DEVCOM-Armaments-Center/SUPI_V3.X/sUPI Electrical/Platform/PB-F-0213 Fusion - SUPI Platform-(src,fab,asm)/ASM-PB-F-0210 Fusion-Platform-[NO VARIATIONS]-A.6/Job1.PDF

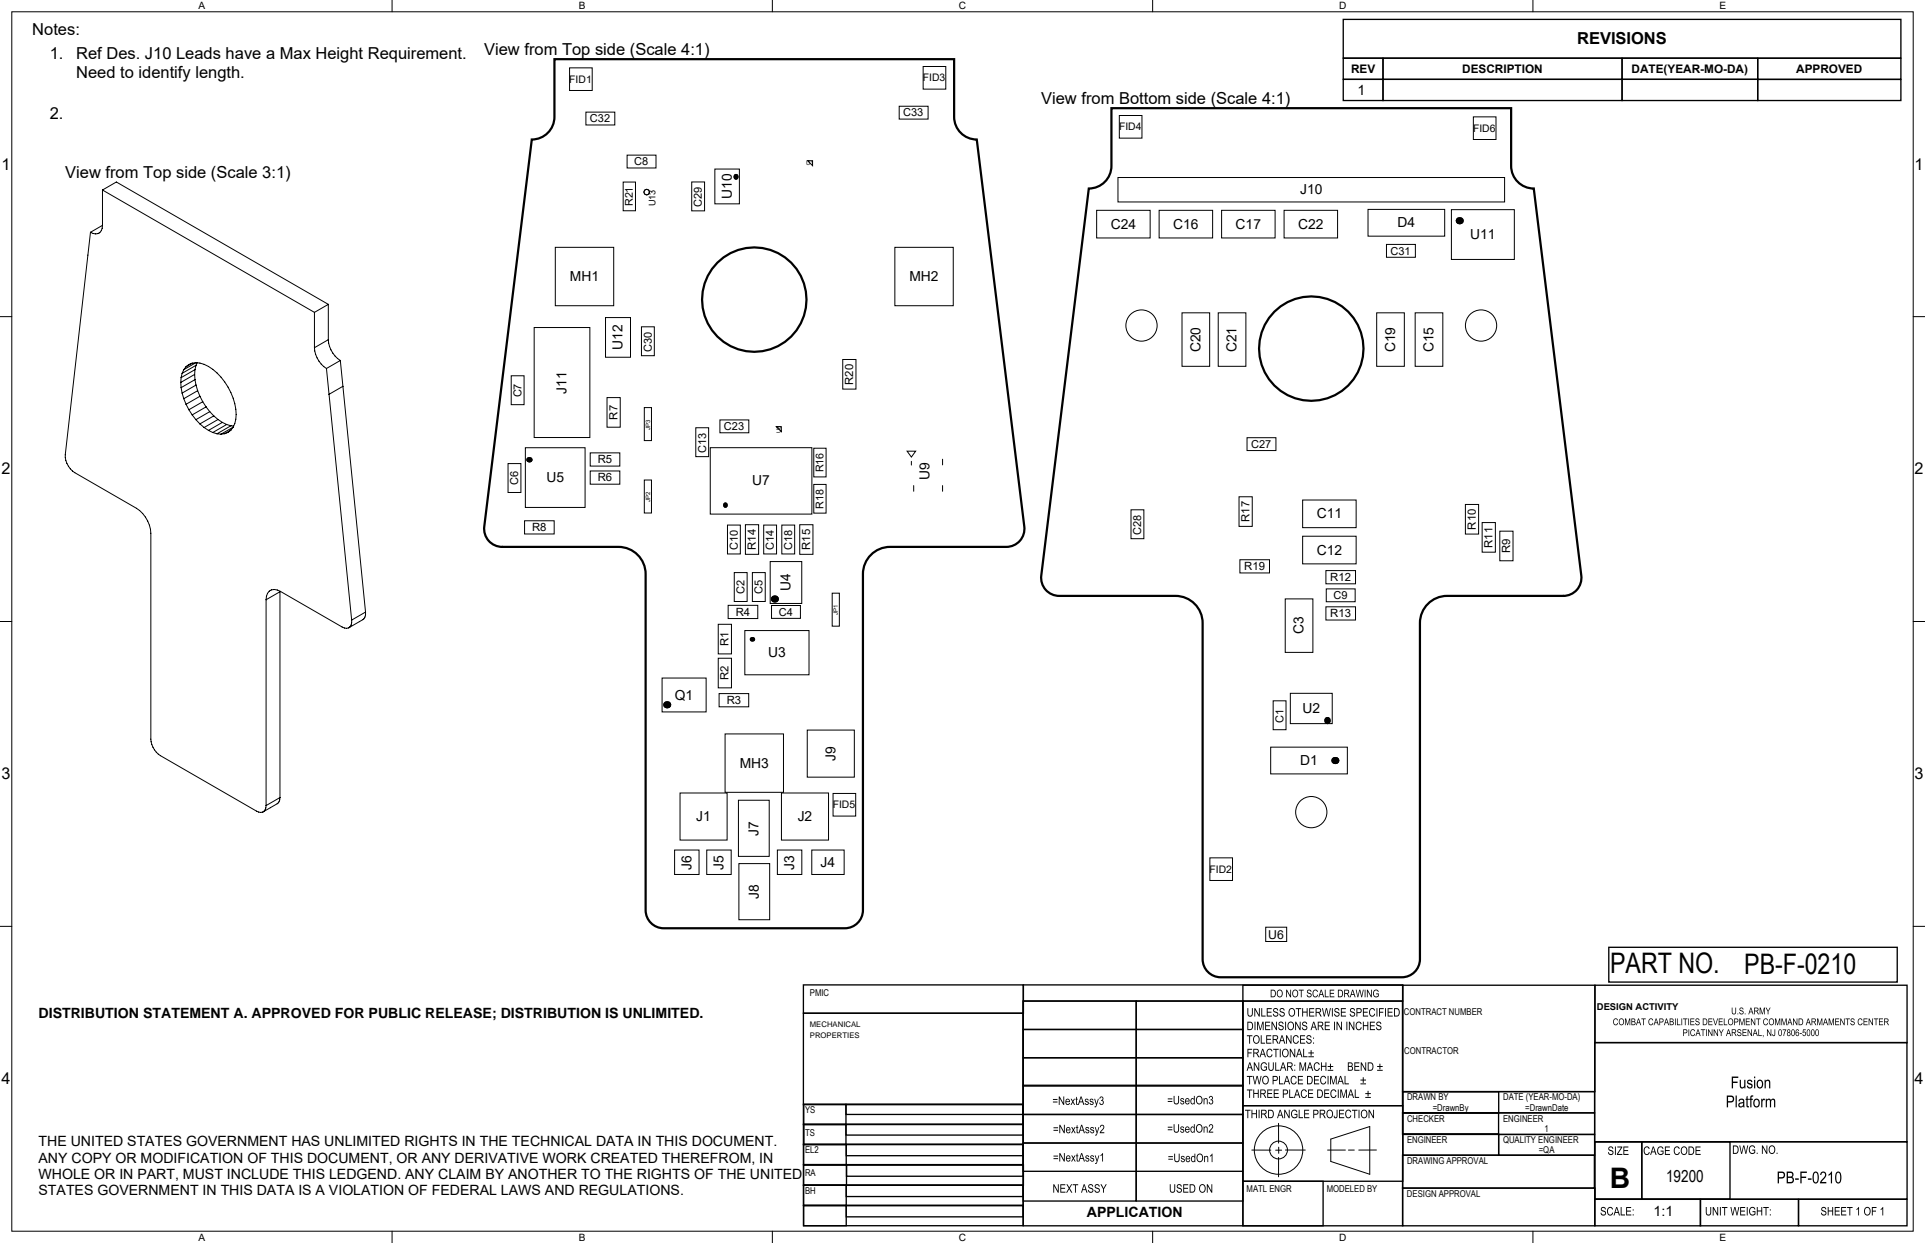
[picture p34: page 1]

Notes:
Ref Des. J10 Leads have a Max Height Requirement.
Need to identify length.

View from Top side (Scale 4:1)

View from Bottom side (Scale 4:1)

View from Top side (Scale 3:1)

DISTRIBUTION STATEMENT A. APPROVED FOR PUBLIC RELEASE; DISTRIBUTION IS UNLIMITED.

DATE (YEAR-MO-DA)
=DrawnDate

THE UNITED STATES GOVERNMENT HAS UNLIMITED RIGHTS IN THE TECHNICAL DATA IN THIS DOCUMENT.
ANY COPY OR MODIFICATION OF THIS DOCUMENT, OR ANY DERIVATIVE WORK CREATED THEREFROM, IN
WHOLE OR IN PART, MUST INCLUDE THIS LEDGEND. ANY CLAIM BY ANOTHER TO THE RIGHTS OF THE UNITED

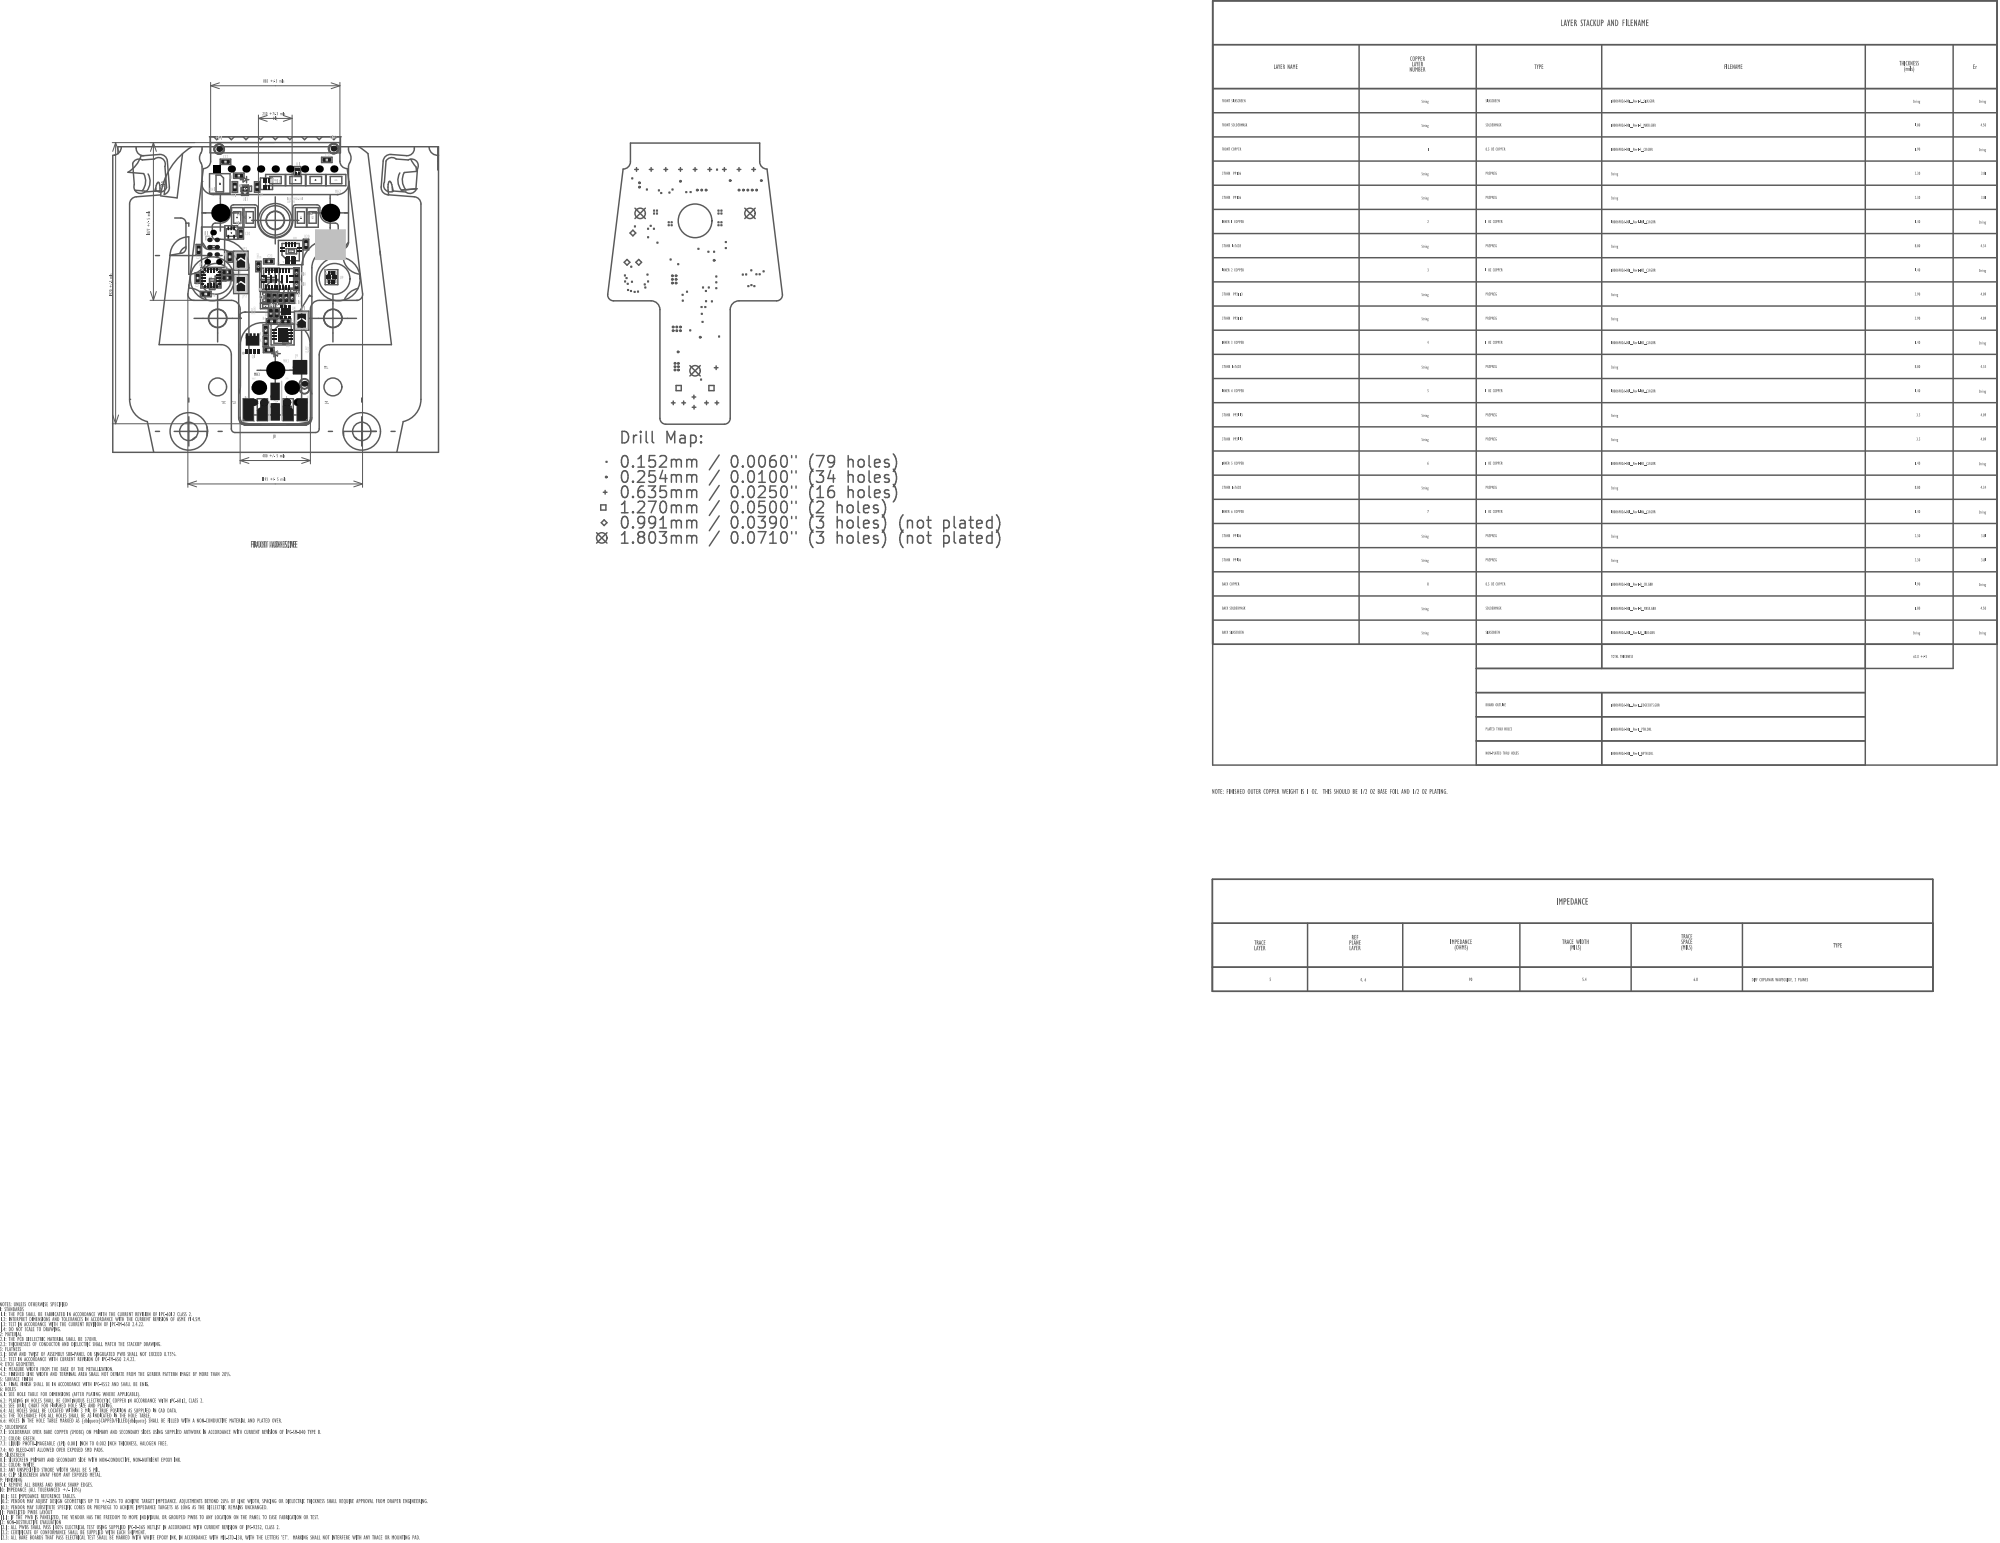
[picture p35: page 2]

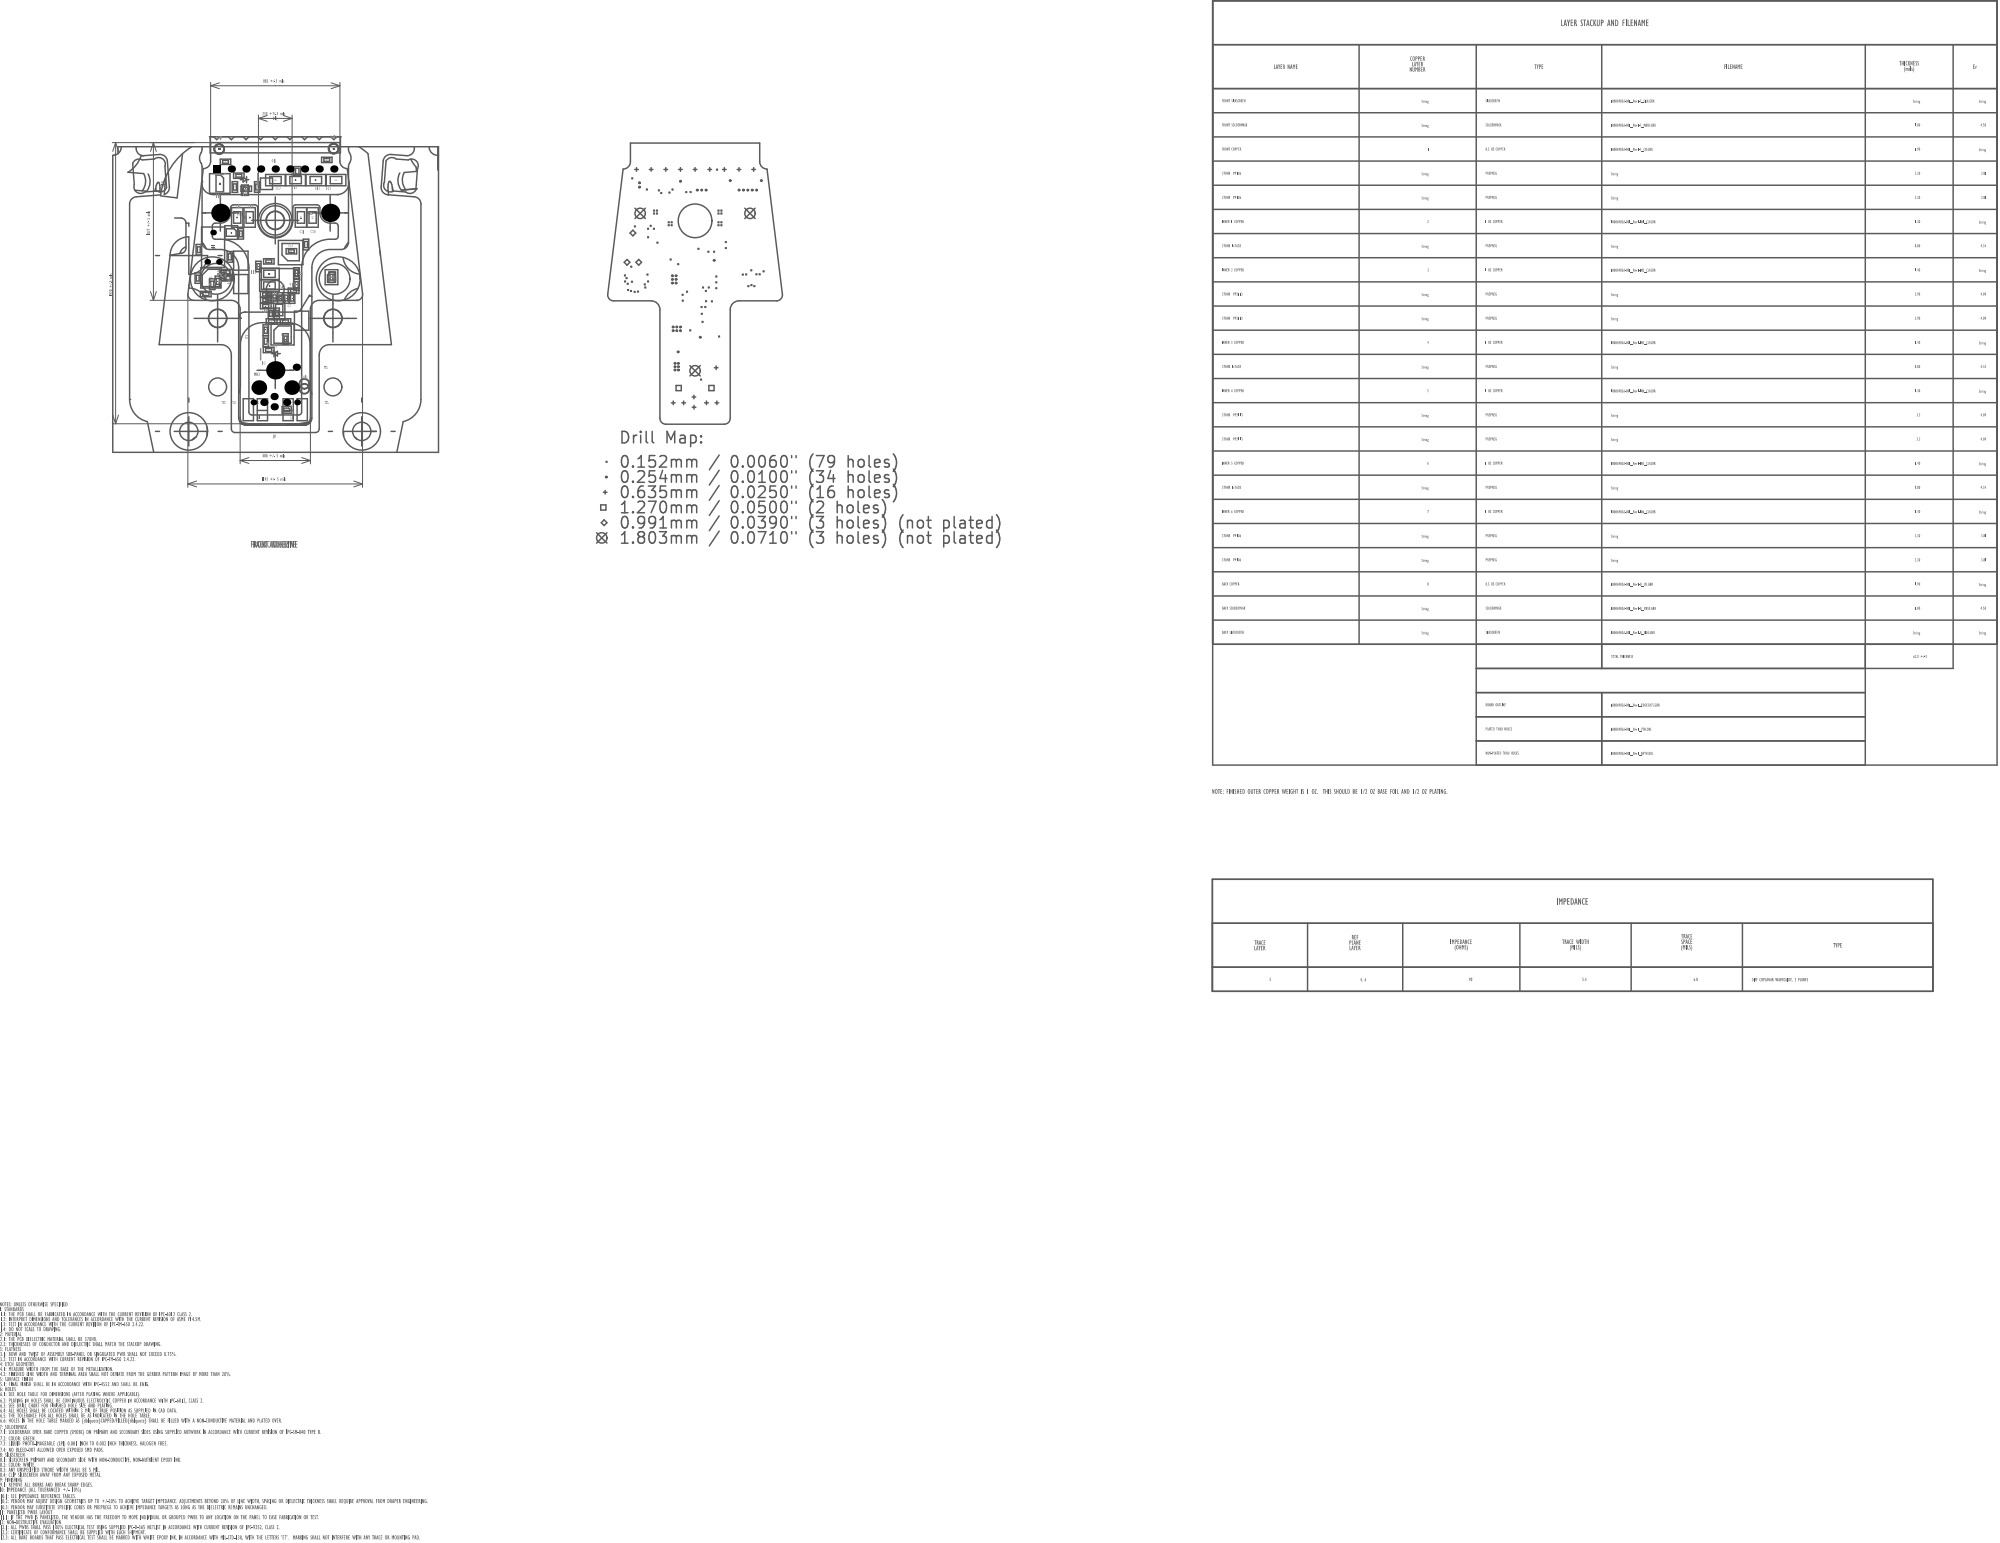
[picture p36: page 3]

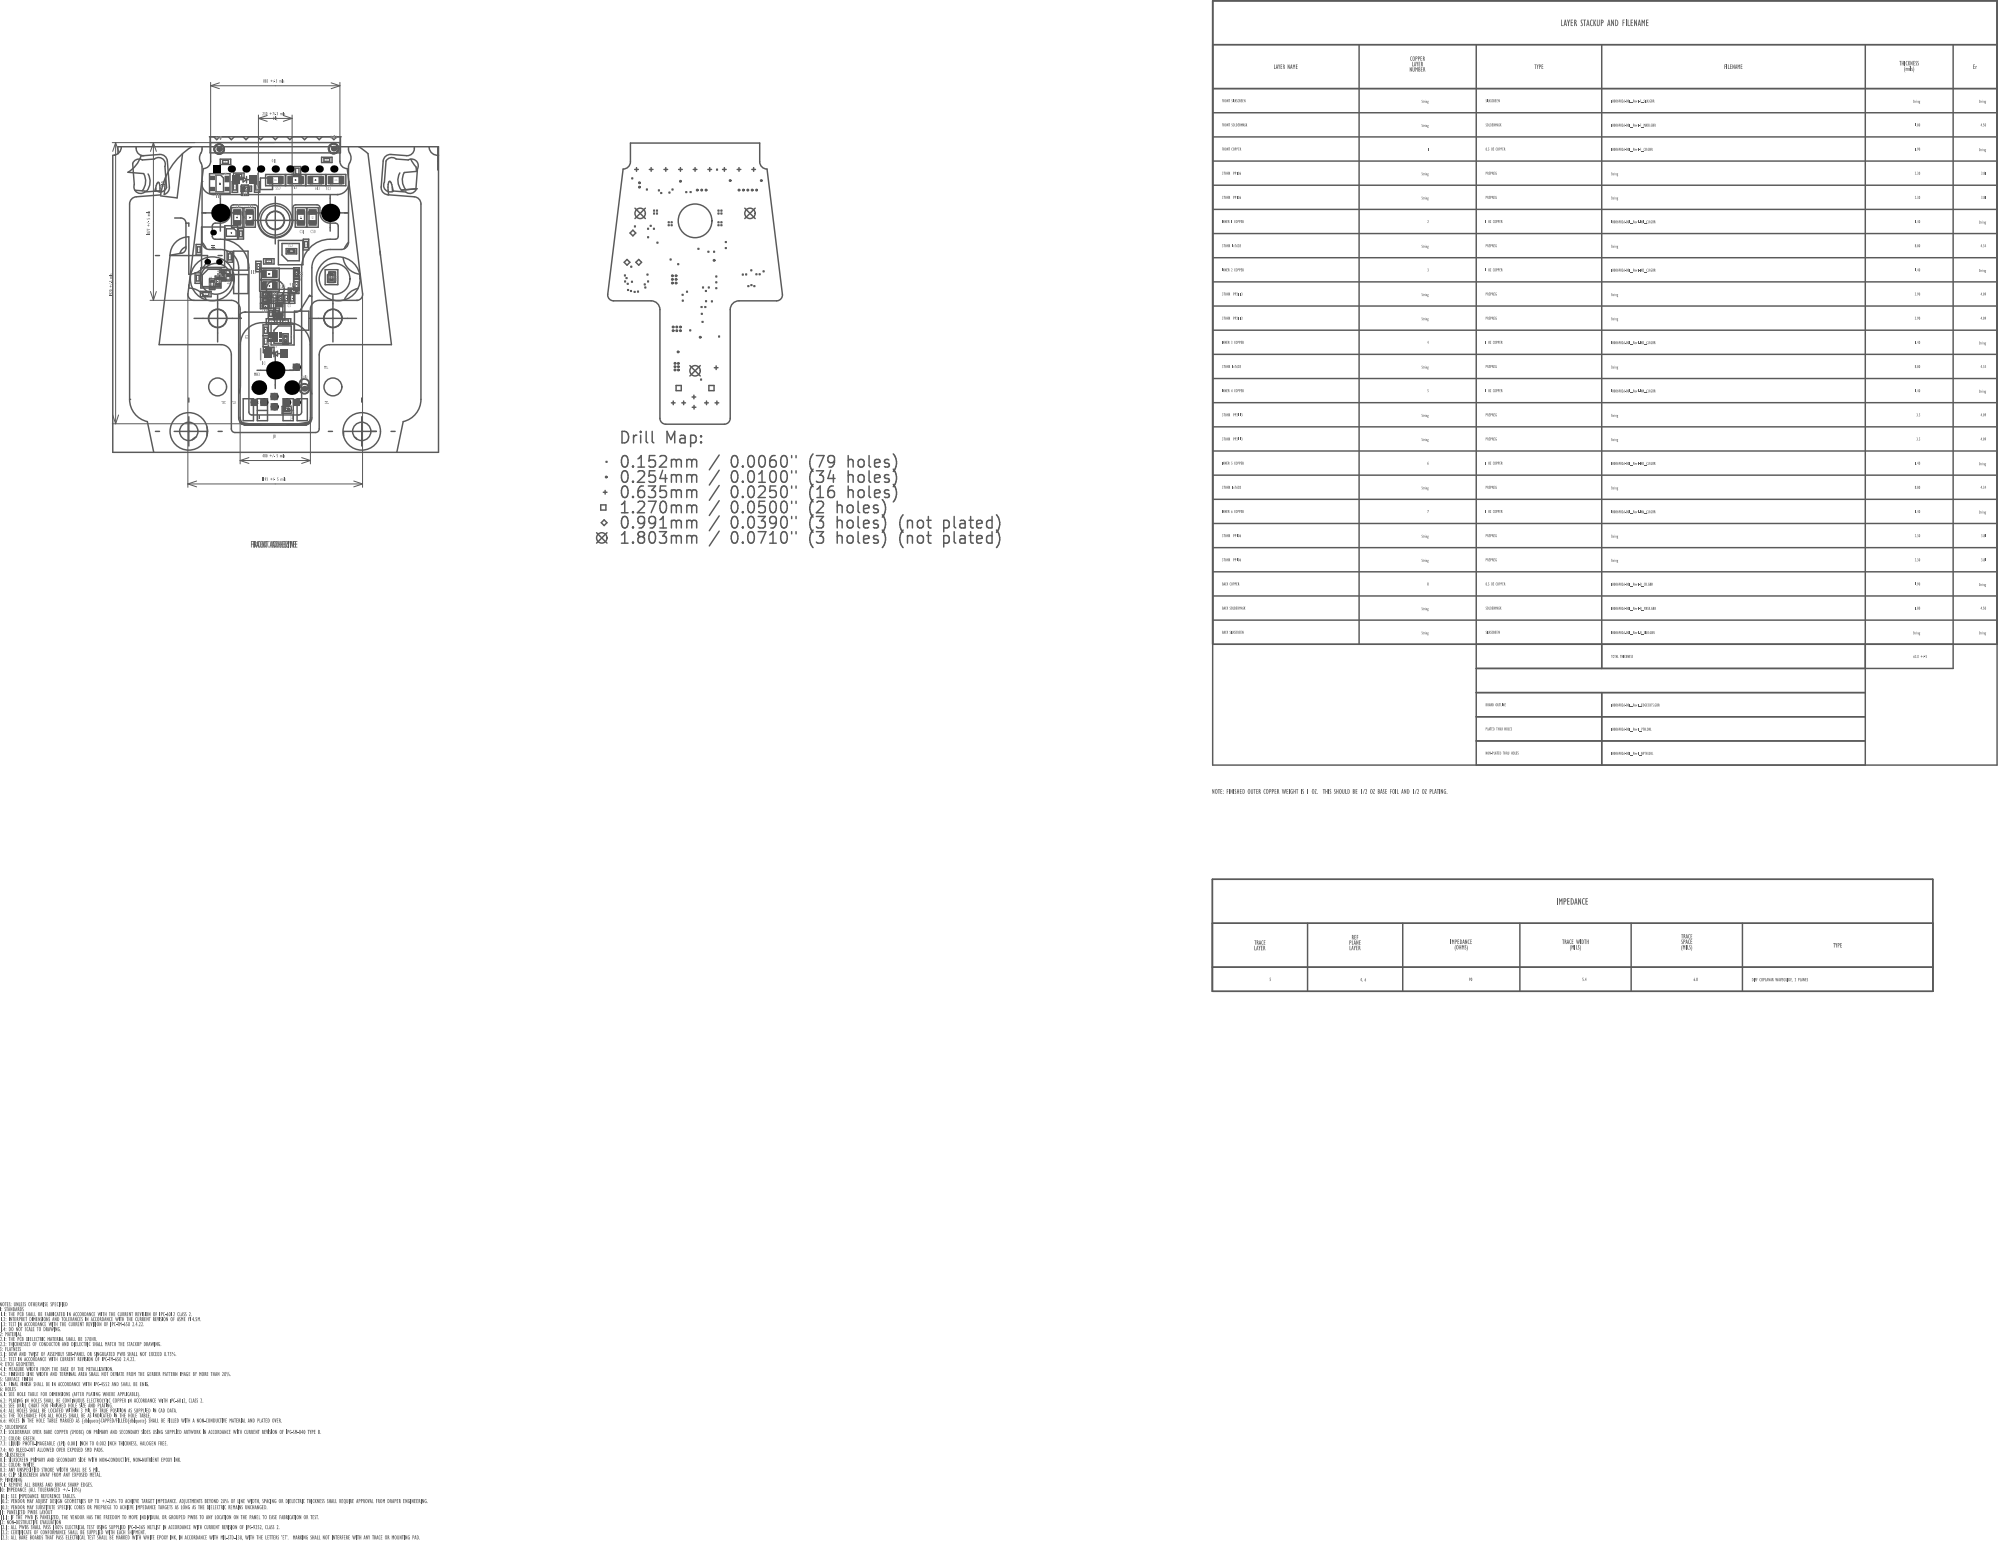
[picture p37: page 9]
